qoq/wiijoy/pics/p1.jpg

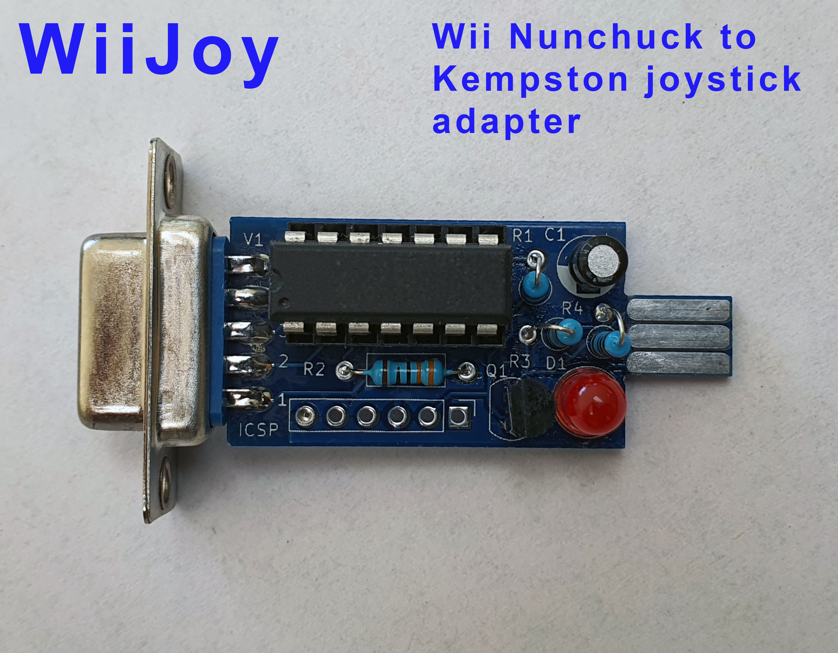
pics/p1.jpg
