qoq/wiijoy/pics/p2.jpg

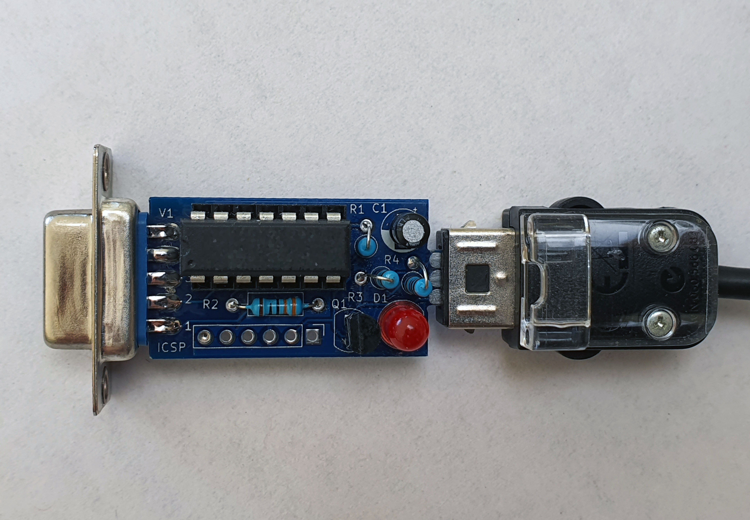
pics/p2.jpg
