qoq/wiijoy/pics/p3.jpg

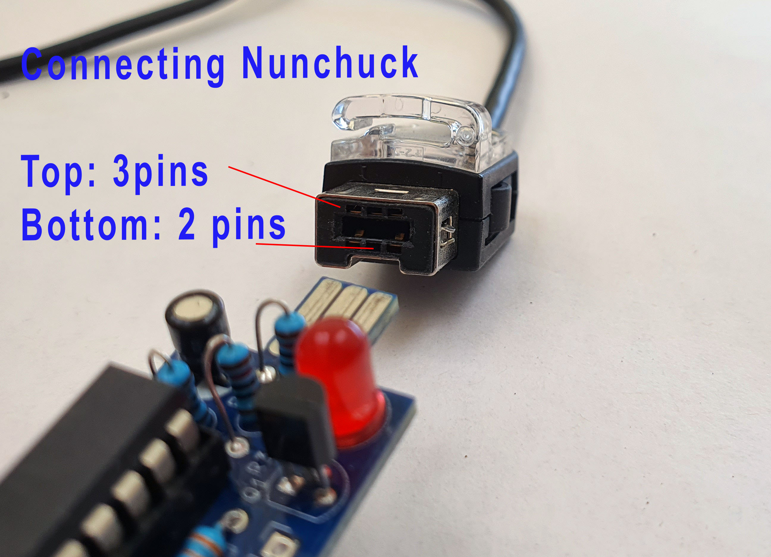
pics/p3.jpg
